baldengineer/Raspberry-Pi-Soft-Power-Controller/firmware/raspberrypi/c-start.c

// install the wiringpi library on your Pi
// And then compile this code
// gcc c-start.c -o c-start -lwiringPi
// copy it to /usr/local/bin

#include <wiringPi.h>

int ioPin = 1; // GPIO18`

int main (void) {
        wiringPiSetup ();
        pinMode (ioPin, OUTPUT);

        digitalWrite (ioPin, HIGH);
        delay (1000);

        return 0;
}
